Schackschuck/KSP/hardware/korry/stl/grades/grade_vista.stl

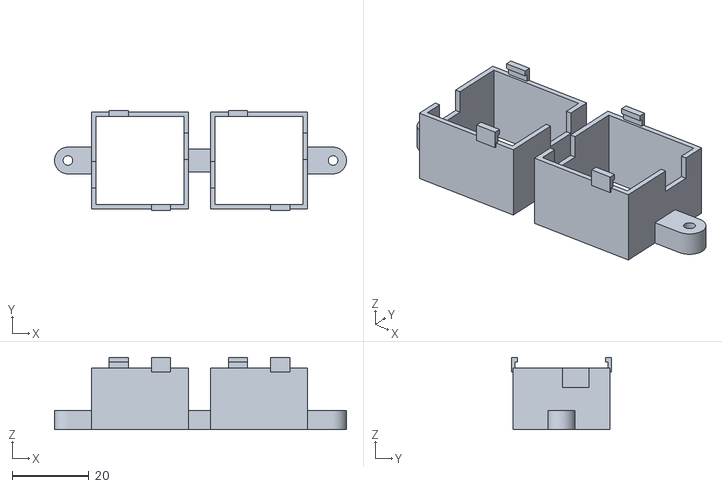
[picture p28: CAD file, 2026-10-02]
hardware/korry/stl/grades/grade_vista.stl
76.0 x 25.9 x 18.8
