Schackschuck/KSP/hardware/korry/stl/legendas/sas_rad_dentro_transparente.stl

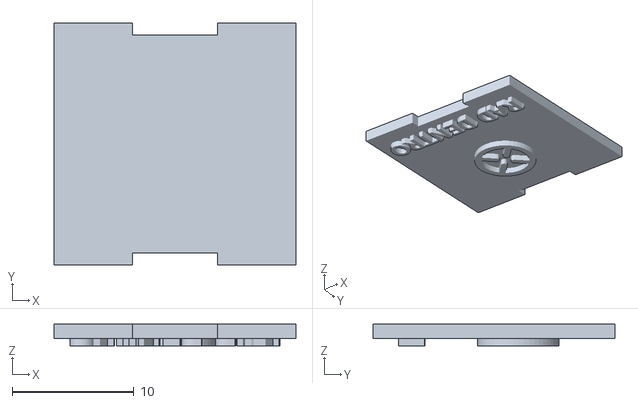
[picture p29: CAD file, 2026-10-02]
hardware/korry/stl/legendas/sas_rad_dentro_transparente.stl
19.9 x 19.9 x 1.80
