Schackschuck/KSP/hardware/korry/stl/grades/grade_deltav.stl

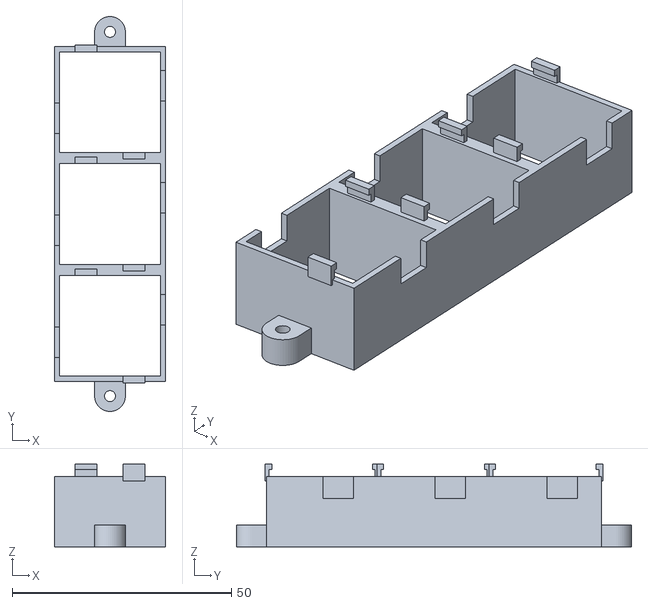
[picture p30: CAD file, 2026-10-02]
hardware/korry/stl/grades/grade_deltav.stl
25.3 x 90.0 x 18.8
