Schackschuck/KSP/hardware/korry/stl/legendas/carga_transparente.stl

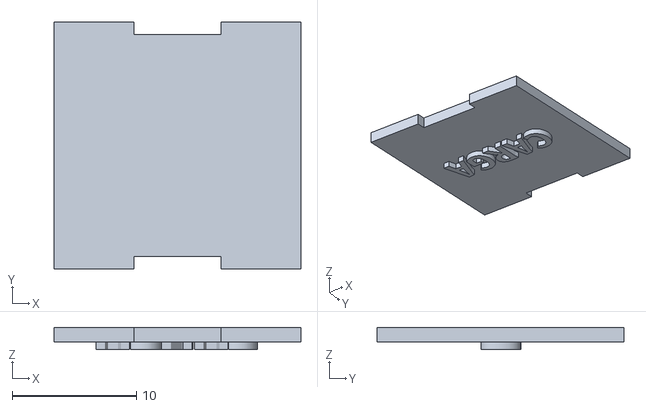
[picture p34: CAD file, 2026-10-02]
hardware/korry/stl/legendas/carga_transparente.stl
19.9 x 19.9 x 1.80
