Schackschuck/KSP/hardware/korry/stl/legendas/sas_preto.stl

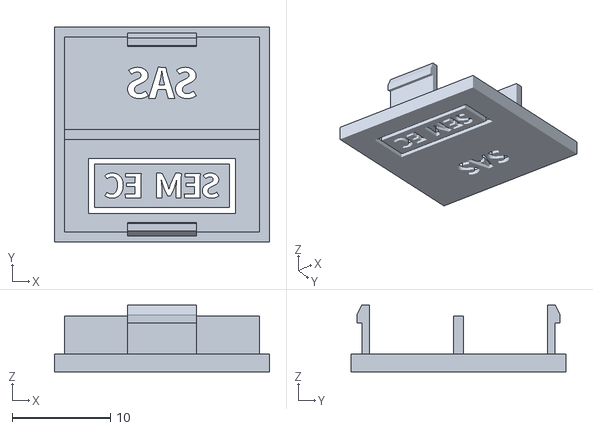
[picture p35: CAD file, 2026-10-02]
hardware/korry/stl/legendas/sas_preto.stl
21.9 x 21.9 x 6.80
