Schackschuck/KSP/hardware/korry/stl/legendas/fbw_transparente.stl

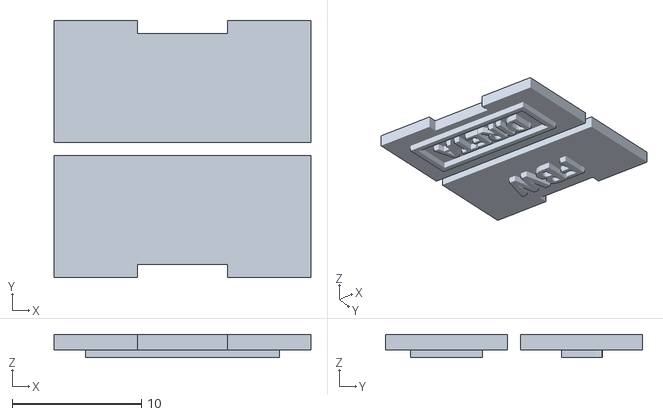
[picture p37: CAD file, 2026-10-02]
hardware/korry/stl/legendas/fbw_transparente.stl
19.9 x 19.9 x 1.80
