Schackschuck/KSP/hardware/korry/stl/legendas/sas_estab_transparente.stl

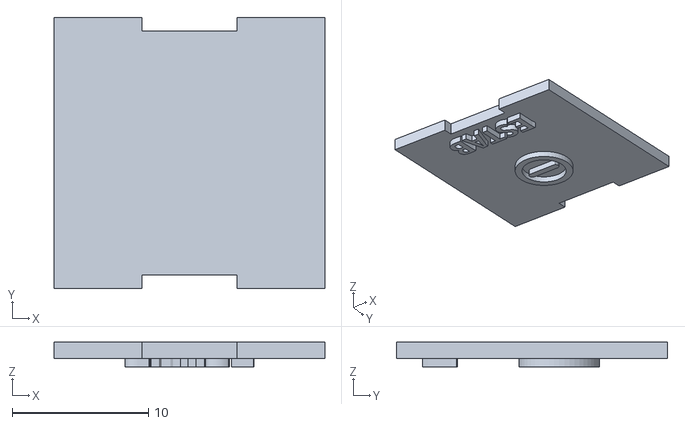
[picture p38: CAD file, 2026-10-02]
hardware/korry/stl/legendas/sas_estab_transparente.stl
19.9 x 19.9 x 1.80
