Schackschuck/KSP/firmware/mfd/tabelas.c

#include "tabelas.h"

const int16_t tabela_seno[901] = {
    0, 29, 57, 86, 114, 143, 172, 200, 229, 257, 286, 315, 343, 372, 400, 429,
    457, 486, 515, 543, 572, 600, 629, 658, 686, 715, 743, 772, 800, 829, 857, 886,
    915, 943, 972, 1000, 1029, 1057, 1086, 1114, 1143, 1171, 1200, 1228, 1257, 1285, 1314, 1342,
    1371, 1399, 1428, 1456, 1485, 1513, 1542, 1570, 1599, 1627, 1656, 1684, 1713, 1741, 1769, 1798,
    1826, 1855, 1883, 1912, 1940, 1968, 1997, 2025, 2053, 2082, 2110, 2139, 2167, 2195, 2224, 2252,
    2280, 2309, 2337, 2365, 2393, 2422, 2450, 2478, 2507, 2535, 2563, 2591, 2619, 2648, 2676, 2704,
    2732, 2761, 2789, 2817, 2845, 2873, 2901, 2929, 2958, 2986, 3014, 3042, 3070, 3098, 3126, 3154,
    3182, 3210, 3238, 3266, 3294, 3322, 3350, 3378, 3406, 3434, 3462, 3490, 3518, 3546, 3574, 3602,
    3630, 3658, 3686, 3713, 3741, 3769, 3797, 3825, 3853, 3880, 3908, 3936, 3964, 3991, 4019, 4047,
    4075, 4102, 4130, 4158, 4185, 4213, 4240, 4268, 4296, 4323, 4351, 4378, 4406, 4434, 4461, 4489,
    4516, 4544, 4571, 4598, 4626, 4653, 4681, 4708, 4735, 4763, 4790, 4818, 4845, 4872, 4899, 4927,
    4954, 4981, 5009, 5036, 5063, 5090, 5117, 5144, 5172, 5199, 5226, 5253, 5280, 5307, 5334, 5361,
    5388, 5415, 5442, 5469, 5496, 5523, 5550, 5577, 5604, 5631, 5657, 5684, 5711, 5738, 5765, 5791,
    5818, 5845, 5872, 5898, 5925, 5952, 5978, 6005, 6031, 6058, 6084, 6111, 6138, 6164, 6191, 6217,
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
    0, 0, 0, 0, 0, 0, 0, 0, 15, 0, 31, 128, 57, 192, 48, 192, 48, 224, 96, 96, 96, 96, 102, 96,
    102, 96, 96, 96, 48, 224, 48, 192, 57, 192, 31, 128, 15, 0, 0, 0, 0, 0, 0, 0, 0, 0, 0, 0,
    0, 0, 0, 0, 0, 0, 0, 0, 15, 0, 63, 0, 51, 0, 3, 0, 3, 0, 3, 0, 3, 0, 3, 0,
    3, 0, 3, 0, 3, 0, 3, 0, 3, 0, 31, 224, 31, 224, 0, 0, 0, 0, 0, 0, 0, 0, 0, 0,
    0, 0, 0, 0, 0, 0, 0, 0, 31, 0, 63, 128, 33, 192, 0, 192, 0, 192, 0, 192, 0, 128, 1, 128,
    3, 0, 6, 0, 12, 0, 24, 0, 48, 0, 127, 192, 127, 192, 0, 0, 0, 0, 0, 0, 0, 0, 0, 0,
    0, 0, 0, 0, 0, 0, 0, 0, 31, 0, 63, 128, 32, 192, 0, 192, 0, 192, 1, 192, 15, 128, 15, 128,
    1, 192, 0, 192, 0, 96, 0, 192, 97, 192, 127, 192, 31, 0, 0, 0, 0, 0, 0, 0, 0, 0, 0, 0,
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
};

const Fonte fonte_grande = {12, 24, 2, dados_grande};
