Schackschuck/KSP/firmware/mfd/lpc2148.h

#ifndef LPC2148_H
#define LPC2148_H

#include <stdint.h>

#define REG(endereco) (*(volatile uint32_t *)(endereco))

#define PINSEL0 REG(0xE002C000)
#define PINSEL1 REG(0xE002C004)
#define PINSEL2 REG(0xE002C014)

#define SCS REG(0xE01FC1A0)
#define MAMCR REG(0xE01FC000)
#define MAMTIM REG(0xE01FC004)
#define PLL0CON REG(0xE01FC080)
#define PLL0CFG REG(0xE01FC084)
#define PLL0STAT REG(0xE01FC088)
#define PLL0FEED REG(0xE01FC08C)
#define VPBDIV REG(0xE01FC100)

#define FIO0DIR REG(0x3FFFC000)
#define FIO0MASK REG(0x3FFFC010)
#define FIO0PIN REG(0x3FFFC014)
#define FIO0SET REG(0x3FFFC018)
#define FIO0CLR REG(0x3FFFC01C)
#define FIO1DIR REG(0x3FFFC020)
#define FIO1MASK REG(0x3FFFC030)
#define FIO1PIN REG(0x3FFFC034)
#define FIO1SET REG(0x3FFFC038)
#define FIO1CLR REG(0x3FFFC03C)

#define U0RBR REG(0xE000C000)
#define U0THR REG(0xE000C000)
#define U0DLL REG(0xE000C000)
#define U0DLM REG(0xE000C004)
#define U0IER REG(0xE000C004)
#define U0IIR REG(0xE000C008)
#define U0FCR REG(0xE000C008)
#define U0LCR REG(0xE000C00C)
#define U0LSR REG(0xE000C014)
#define U0FDR REG(0xE000C028)

#define T0TCR REG(0xE0004004)
#define T0TC REG(0xE0004008)
#define T0PR REG(0xE000400C)

#define AD0CR REG(0xE0034000)
#define AD0GDR REG(0xE0034004)

#define VICINTSELECT REG(0xFFFFF00C)
#define VICINTENABLE REG(0xFFFFF010)
#define VICVECTADDR REG(0xFFFFF030)
#define VICVECTADDR0 REG(0xFFFFF100)
#define VICVECTCNTL0 REG(0xFFFFF200)

#define VIC_UART0 6

#define CCLK_KHZ 60000u

#endif
